lucky-mango/minecraft_compass/images/animation/Compass_Proctex_Needle_Points.gif

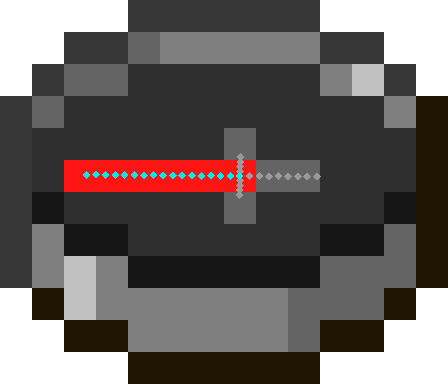
images/animation/Compass_Proctex_Needle_Points.gif
