lucky-mango/minecraft_compass/images/indexedPixels/0.png

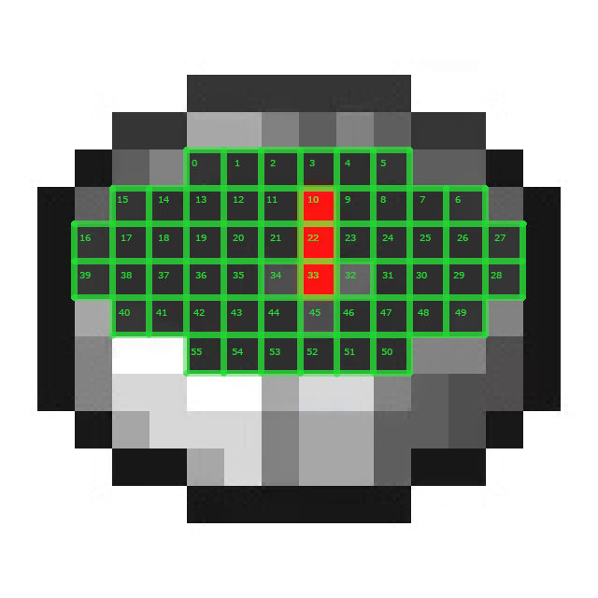
images/indexedPixels/0.png
