lucky-mango/minecraft_compass/images/indexedPixels/1.png

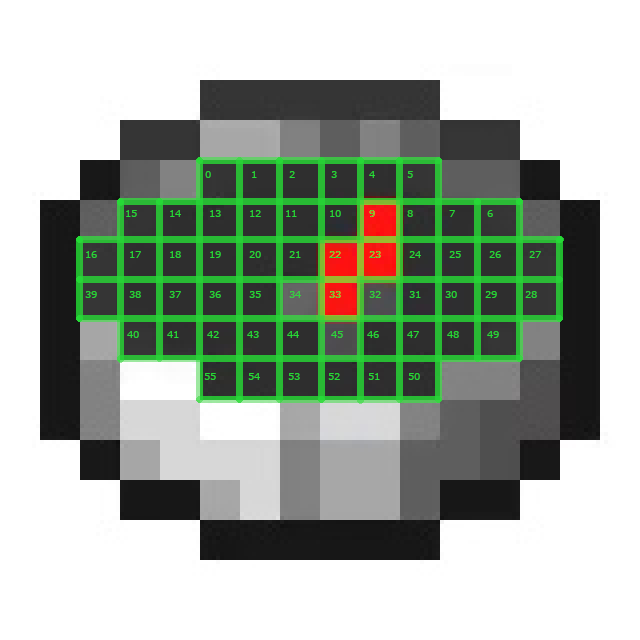
images/indexedPixels/1.png
