lucky-mango/minecraft_compass/images/inGame/Screenshot (223).png

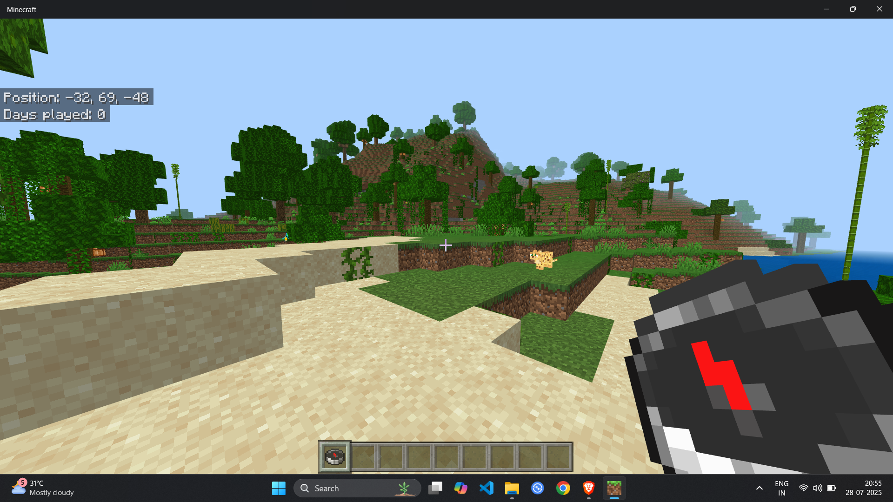
images/inGame/Screenshot (223).png
