lucky-mango/minecraft_compass/images/inGame/Screenshot (224).png

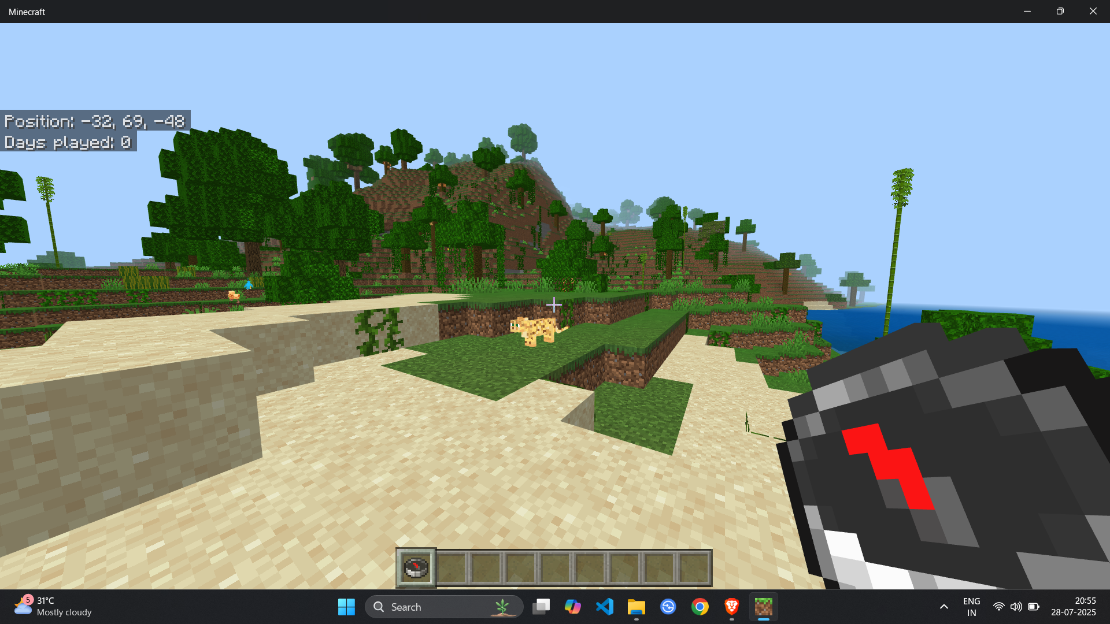
images/inGame/Screenshot (224).png
