lucky-mango/minecraft_compass/images/inGame/Screenshot (225).png

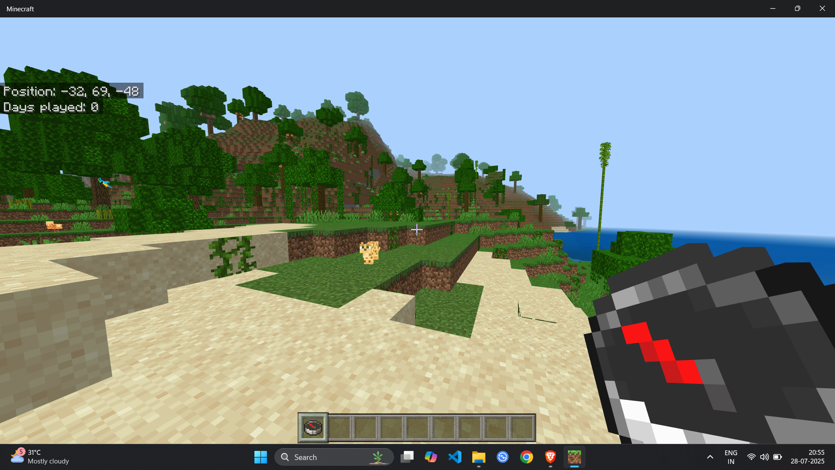
images/inGame/Screenshot (225).png
