lucky-mango/minecraft_compass/images/inGame/Screenshot (226).png

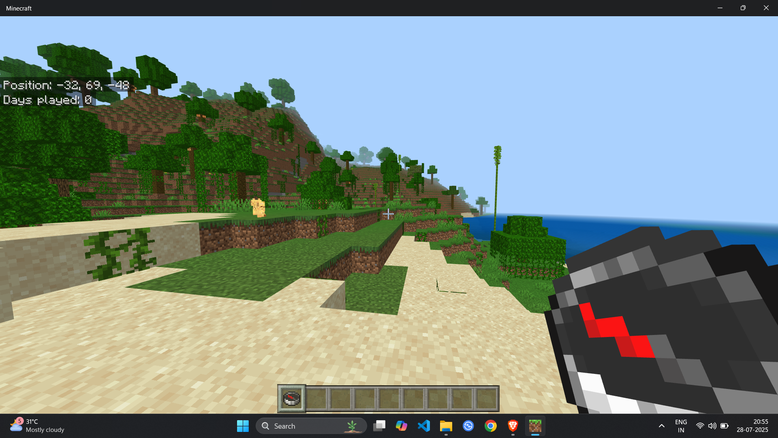
images/inGame/Screenshot (226).png
