lucky-mango/minecraft_compass/images/inGame/Screenshot (227).png

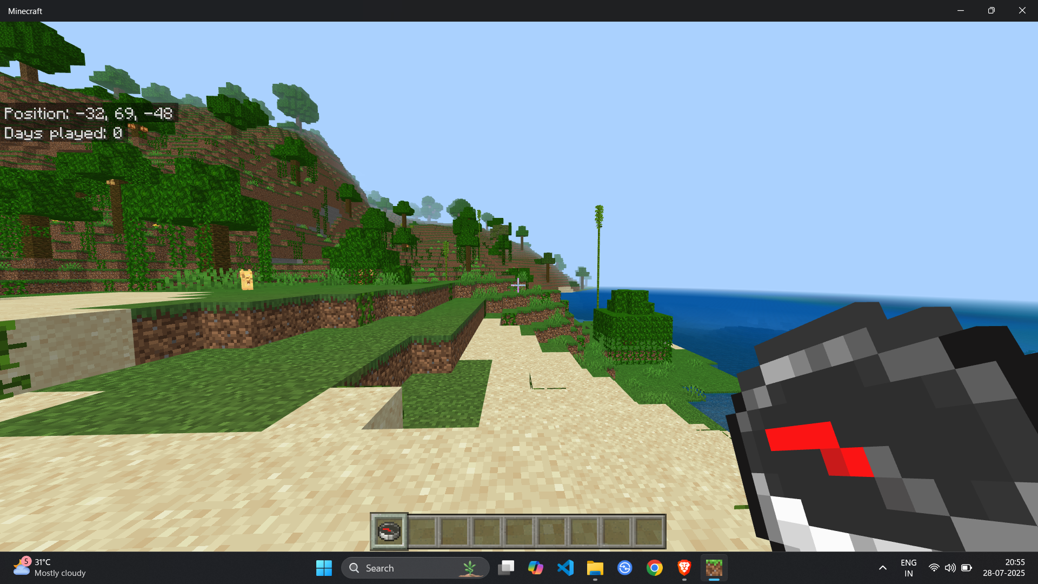
images/inGame/Screenshot (227).png
