lucky-mango/minecraft_compass/images/inGame/Screenshot (228).png

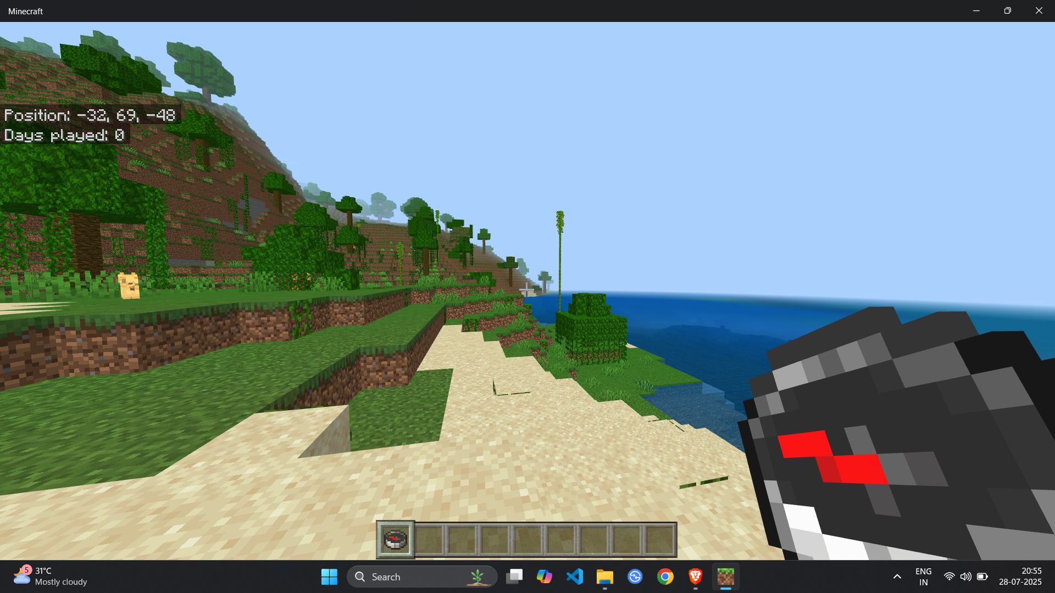
images/inGame/Screenshot (228).png
