lucky-mango/minecraft_compass/images/inGame/Screenshot (230).png

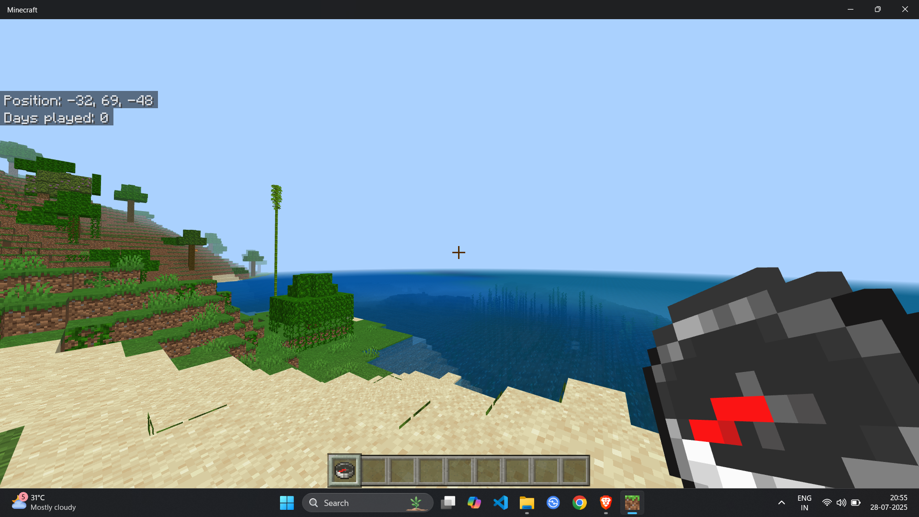
images/inGame/Screenshot (230).png
