lucky-mango/minecraft_compass/images/inGame/Screenshot (231).png

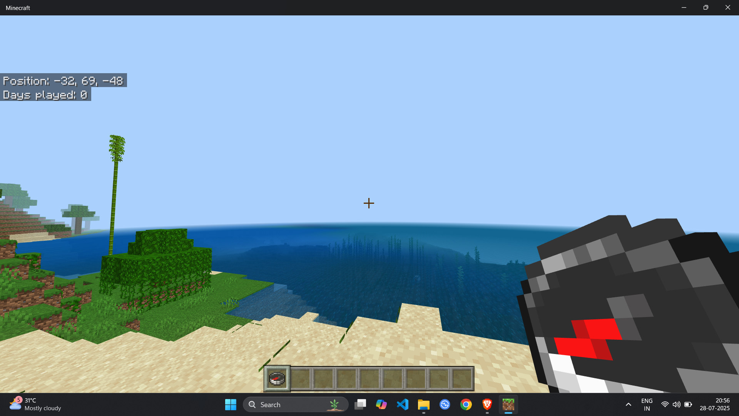
images/inGame/Screenshot (231).png
