lucky-mango/minecraft_compass/images/inGame/Screenshot (232).png

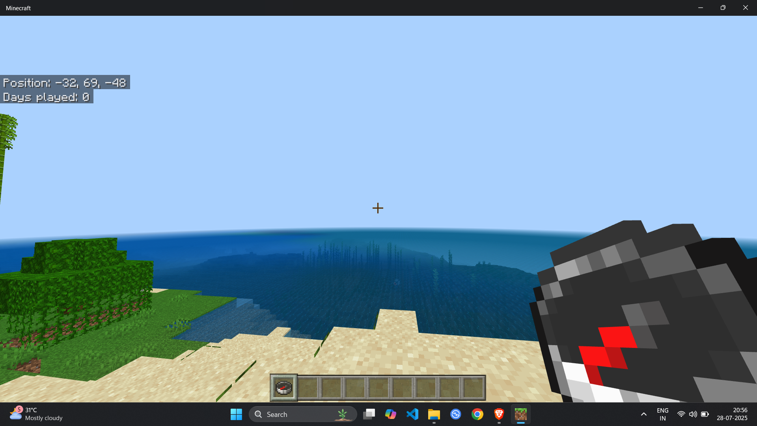
images/inGame/Screenshot (232).png
