lucky-mango/minecraft_compass/images/inGame/Screenshot (233).png

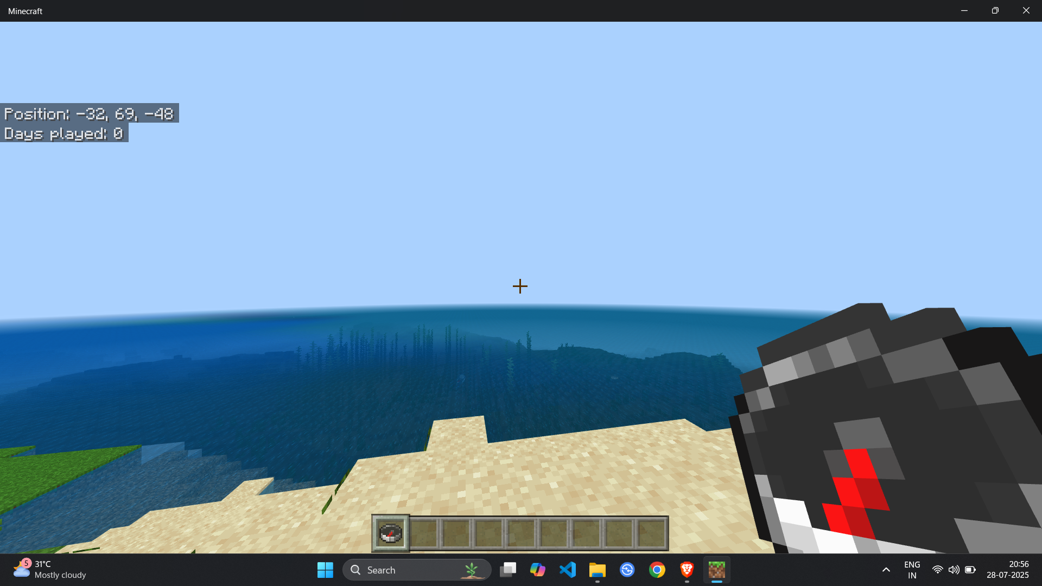
images/inGame/Screenshot (233).png
