lucky-mango/minecraft_compass/images/inGame/Screenshot (235).png

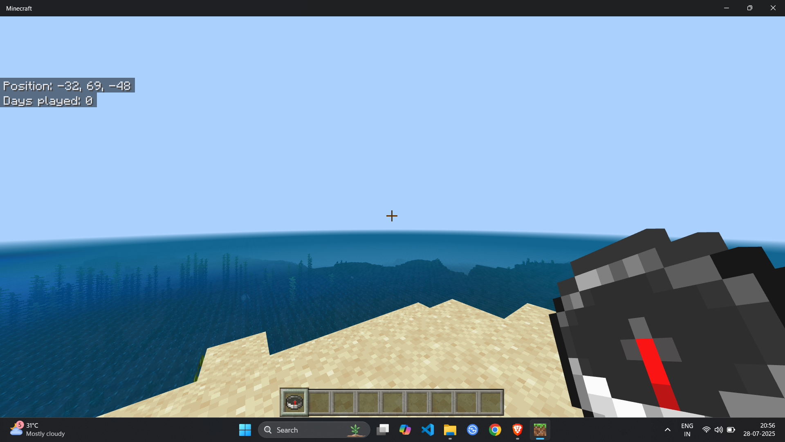
images/inGame/Screenshot (235).png
