lucky-mango/minecraft_compass/images/inGame/Screenshot (238).png

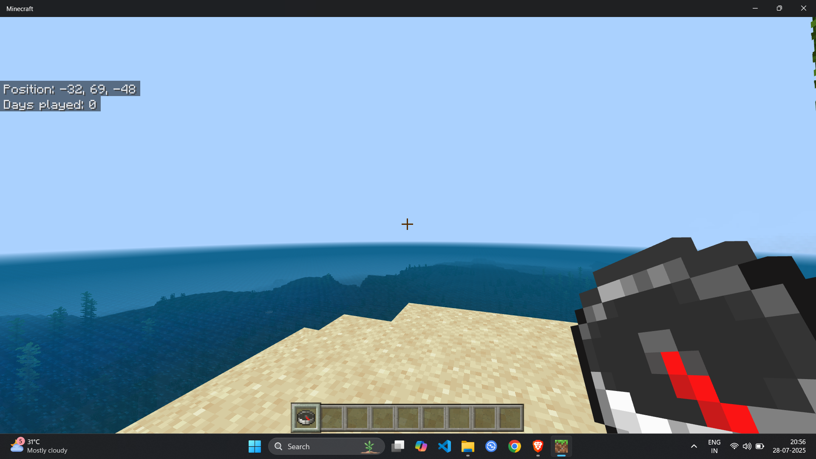
images/inGame/Screenshot (238).png
