lucky-mango/minecraft_compass/images/inGame/Screenshot (239).png

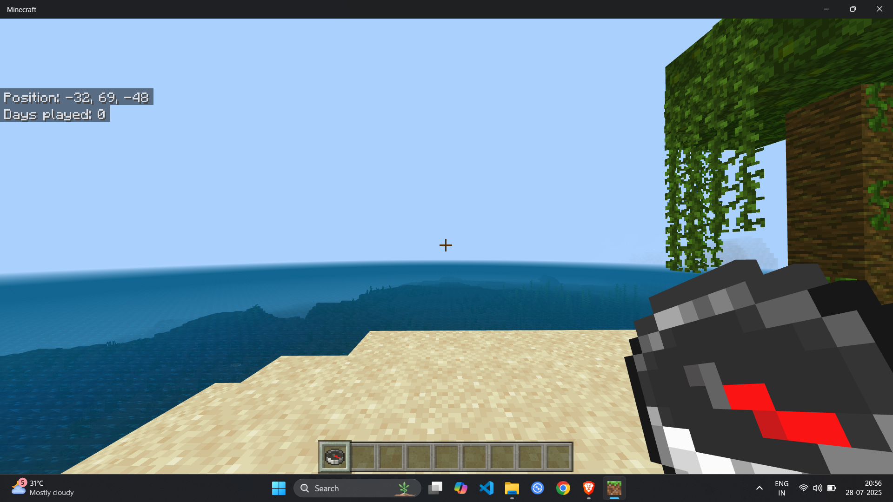
images/inGame/Screenshot (239).png
