lucky-mango/minecraft_compass/images/inGame/Screenshot (240).png

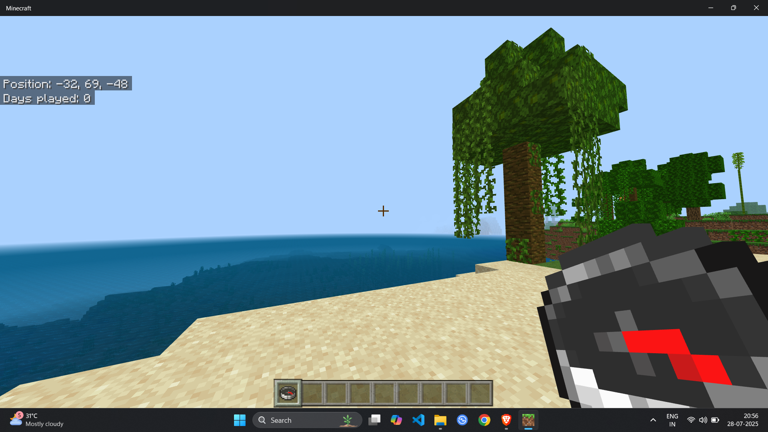
images/inGame/Screenshot (240).png
