lucky-mango/minecraft_compass/images/inGame/Screenshot (241).png

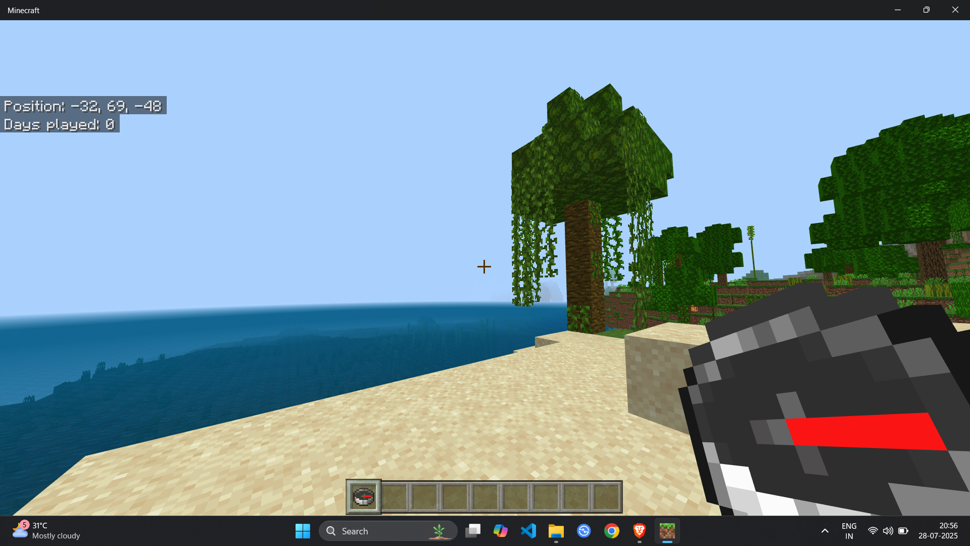
images/inGame/Screenshot (241).png
