lucky-mango/minecraft_compass/images/inGame/Screenshot (242).png

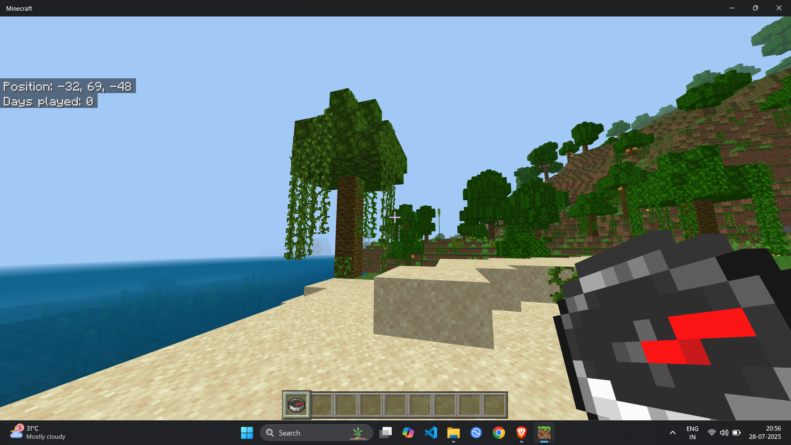
images/inGame/Screenshot (242).png
