lucky-mango/minecraft_compass/images/inGame/Screenshot (243).png

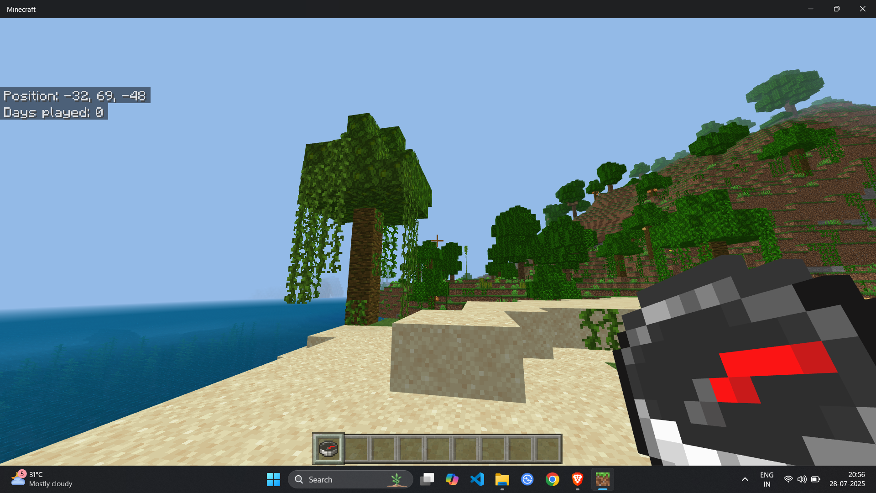
images/inGame/Screenshot (243).png
