lucky-mango/minecraft_compass/images/inGame/Screenshot (246).png

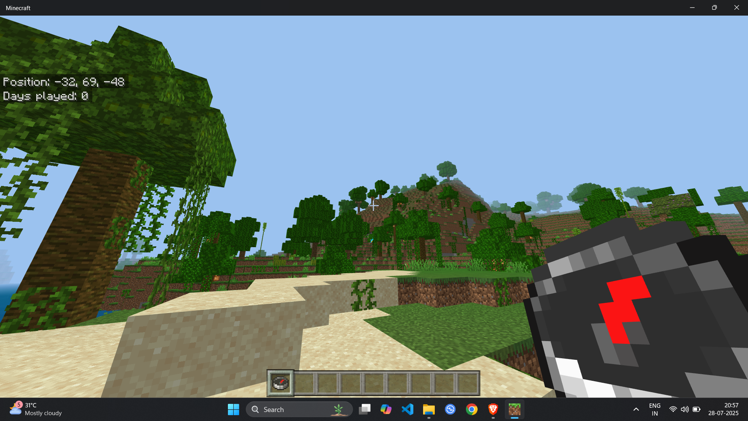
images/inGame/Screenshot (246).png
