lucky-mango/minecraft_compass/images/inGame/Screenshot (247).png

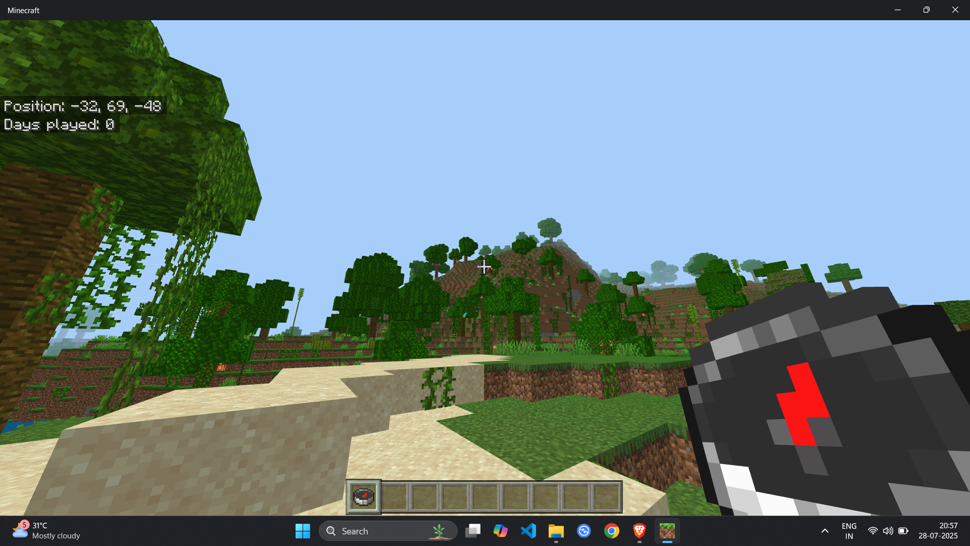
images/inGame/Screenshot (247).png
