lucky-mango/minecraft_compass/images/inGame/Screenshot (248).png

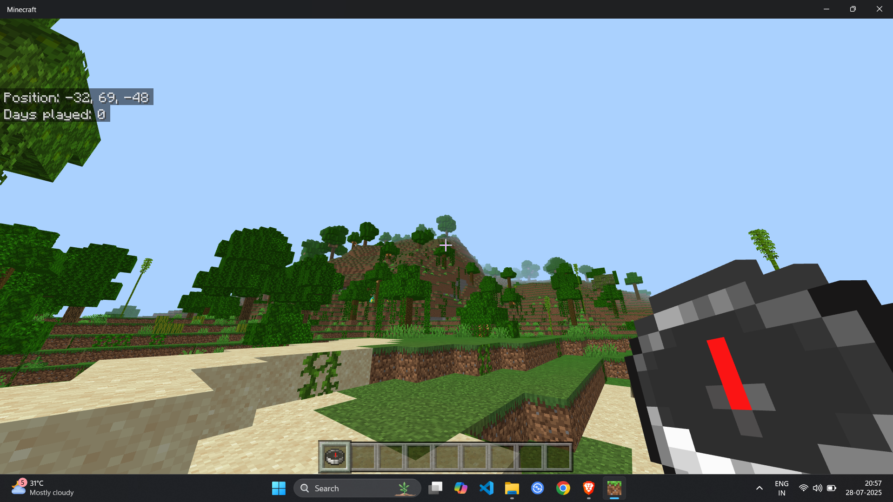
images/inGame/Screenshot (248).png
