lucky-mango/minecraft_compass/3D_models/SMD WS2812B Mini.step

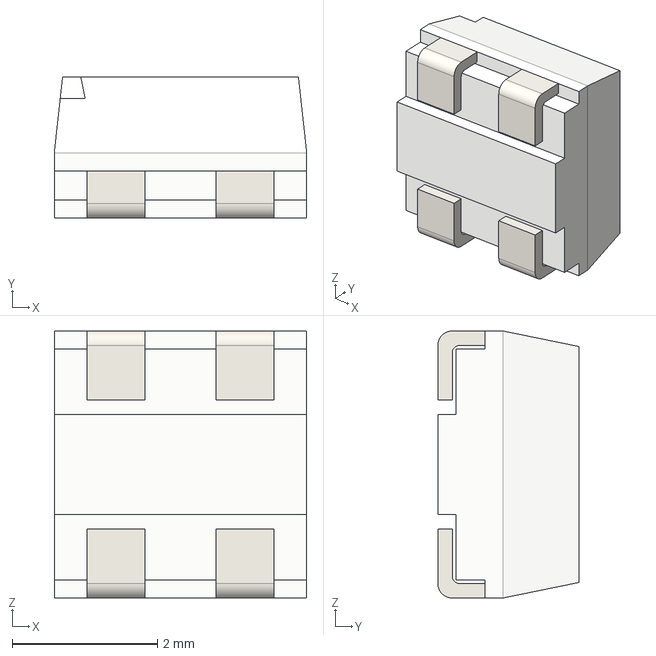
[picture p48: CAD file, 2026-05-20]
3D_models/SMD WS2812B Mini.step
3.48 x 1.95 x 3.68 mm
