lucky-mango/minecraft_compass/3D_models/SM03B-SRSS-TB (LF)(SN).STEP

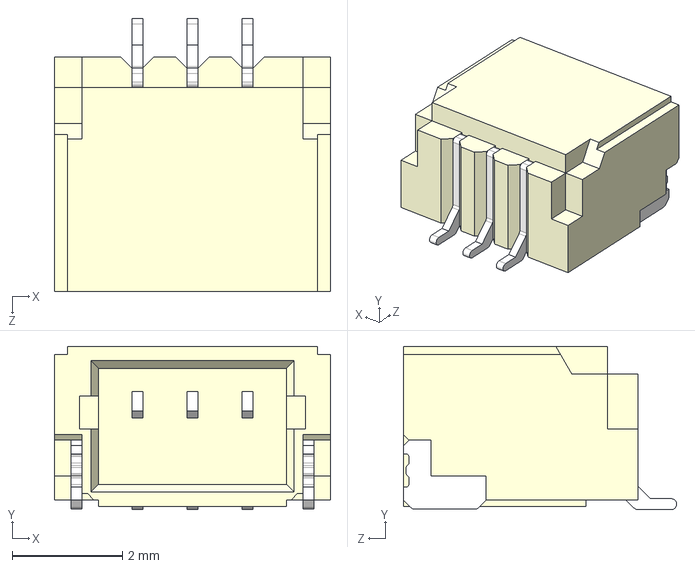
[picture p49: CAD file, 2026-05-20]
3D_models/SM03B-SRSS-TB (LF)(SN).STEP
5.00 x 2.96 x 4.95 mm
